AlfonsoJLuna/openhandheld-mx/Images/1.png

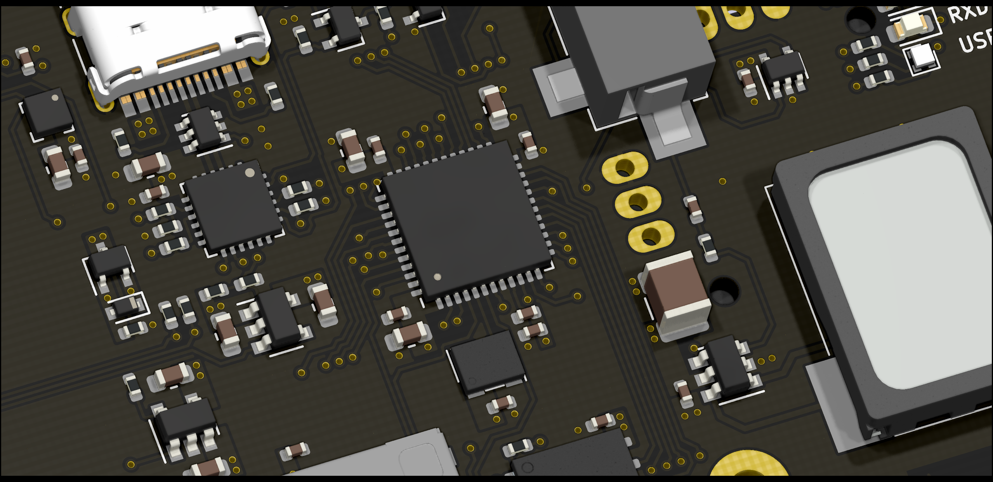
Images/1.png
