AlfonsoJLuna/openhandheld-mx/Images/3.png

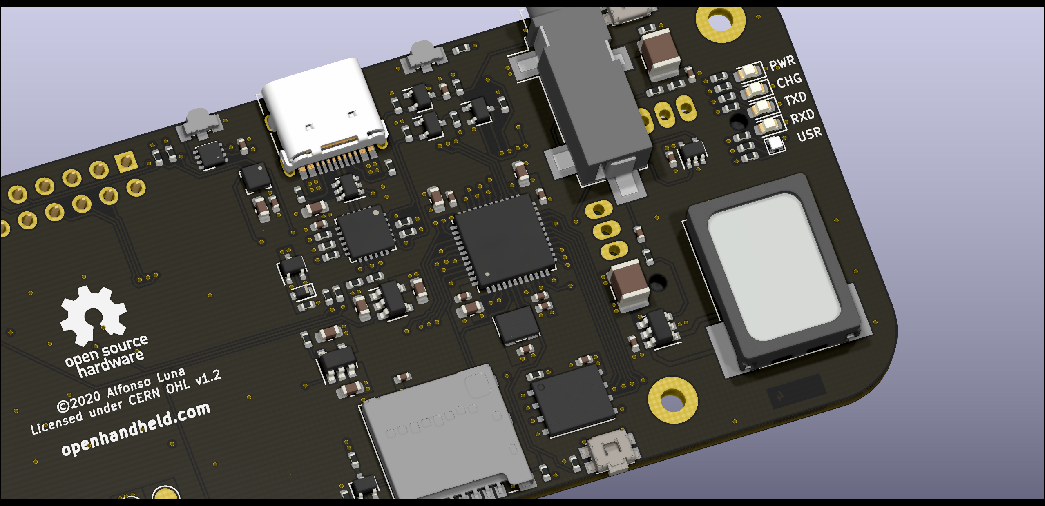
Images/3.png
