AlfonsoJLuna/openhandheld-mx/Images/4.png

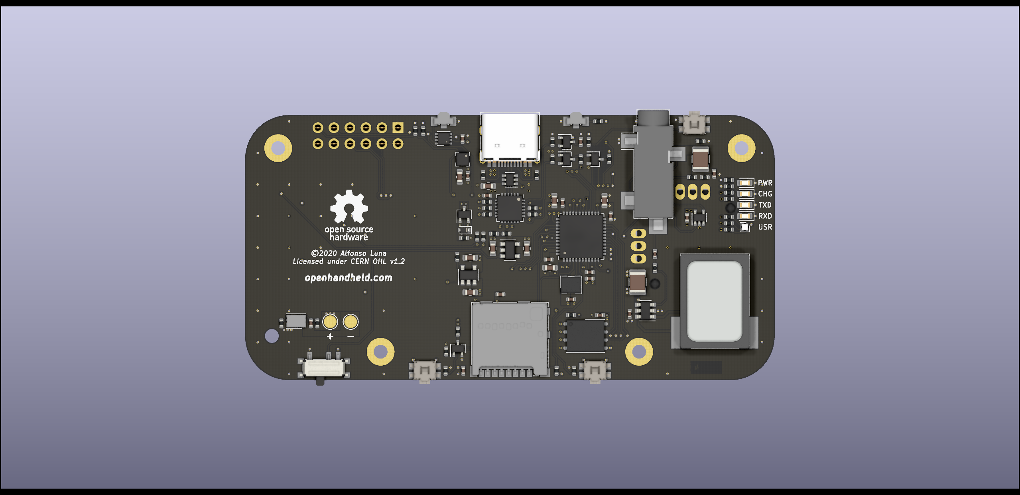
Images/4.png
