AlfonsoJLuna/openhandheld-mx/Images/5.png

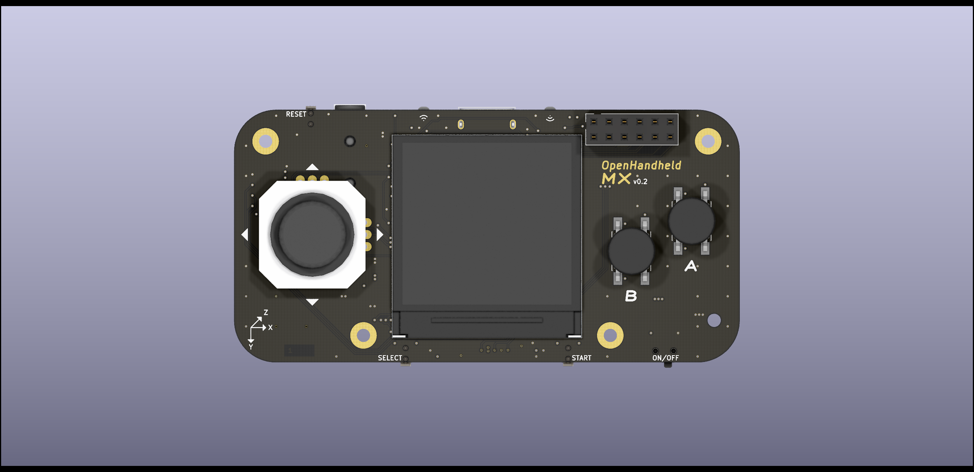
Images/5.png
