AlfonsoJLuna/openhandheld-mx/Images/8.png

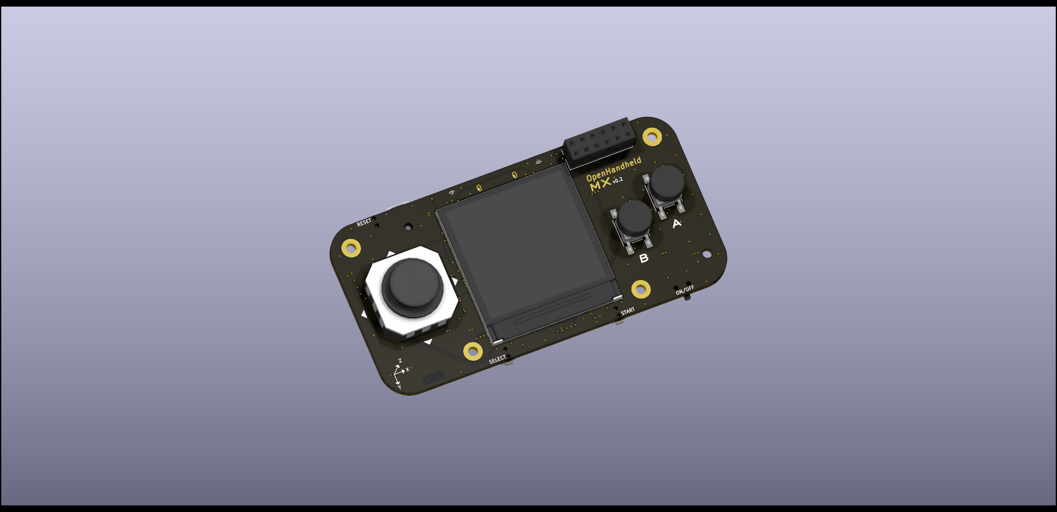
Images/8.png
