AlfonsoJLuna/openhandheld-mx/Images/10.png

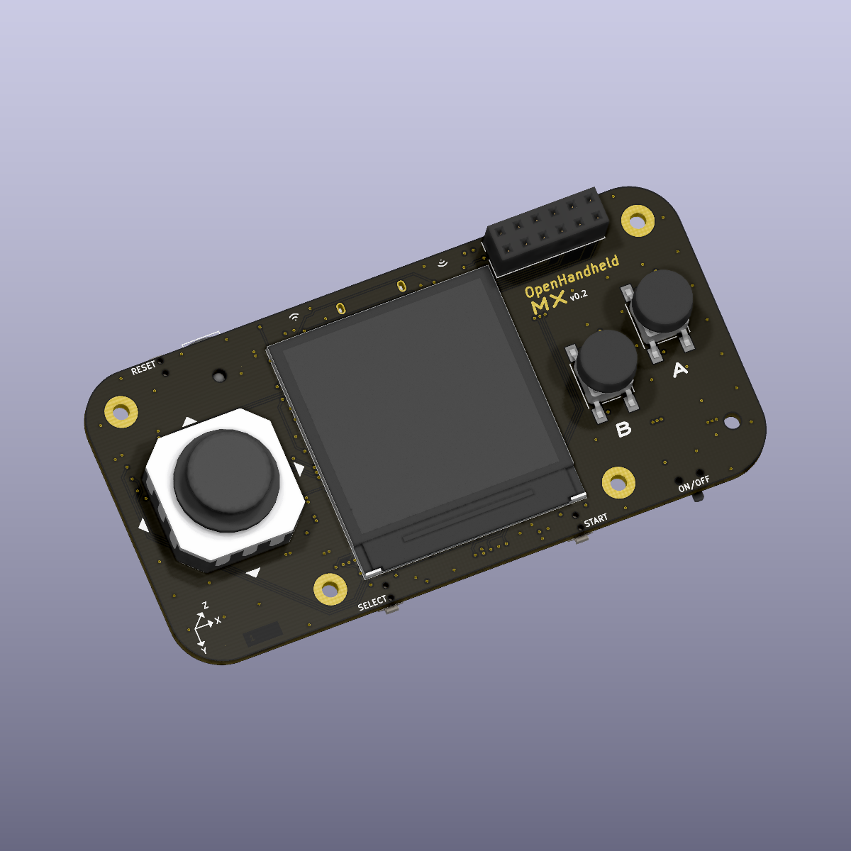
Images/10.png
