AlfonsoJLuna/openhandheld-mx/Images/11.png

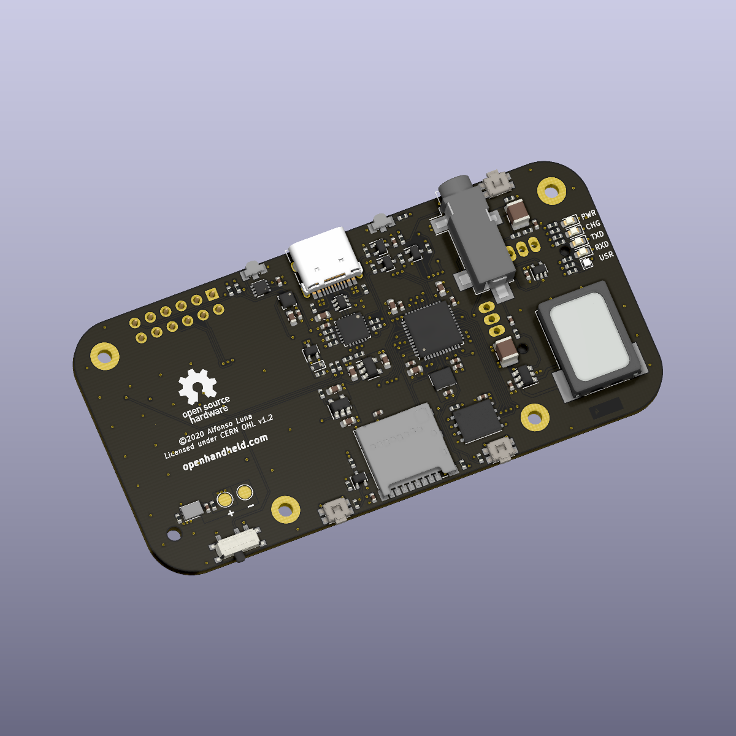
Images/11.png
