AlfonsoJLuna/openhandheld-mx/Images/12.png

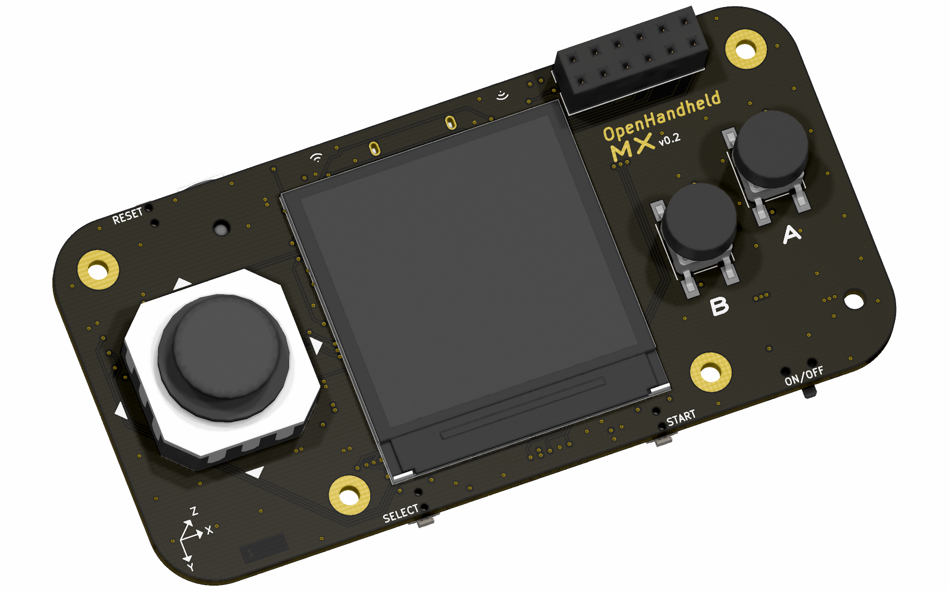
Images/12.png
