AlfonsoJLuna/openhandheld-mx/Images/13.png

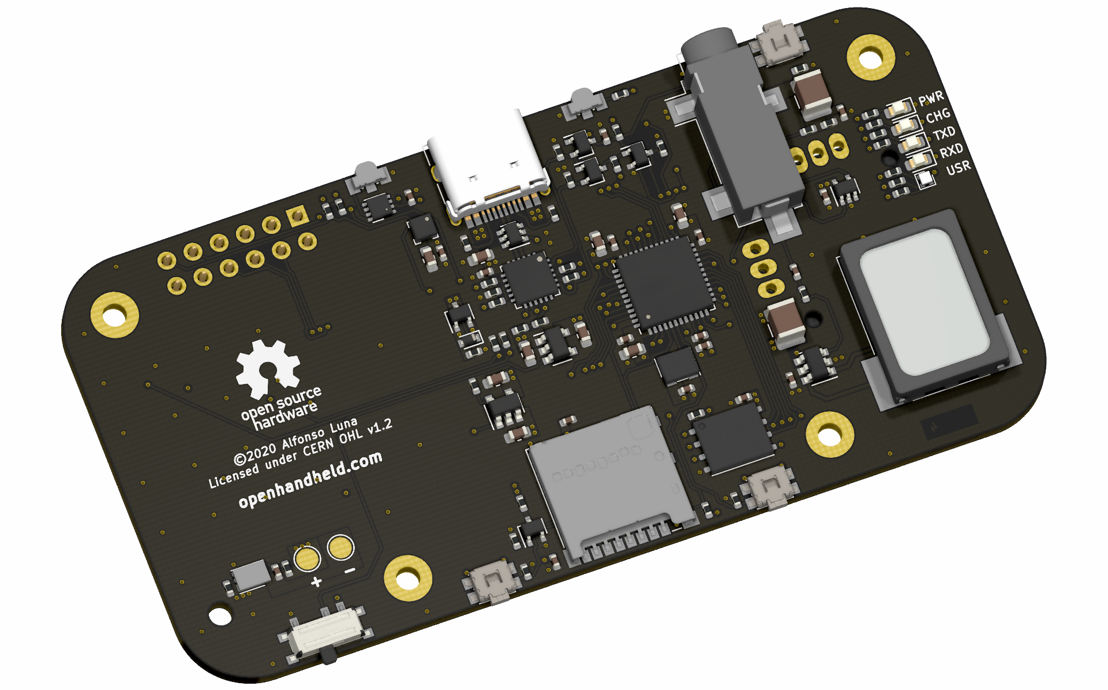
Images/13.png
