AlfonsoJLuna/openhandheld-mx/Images/16.png

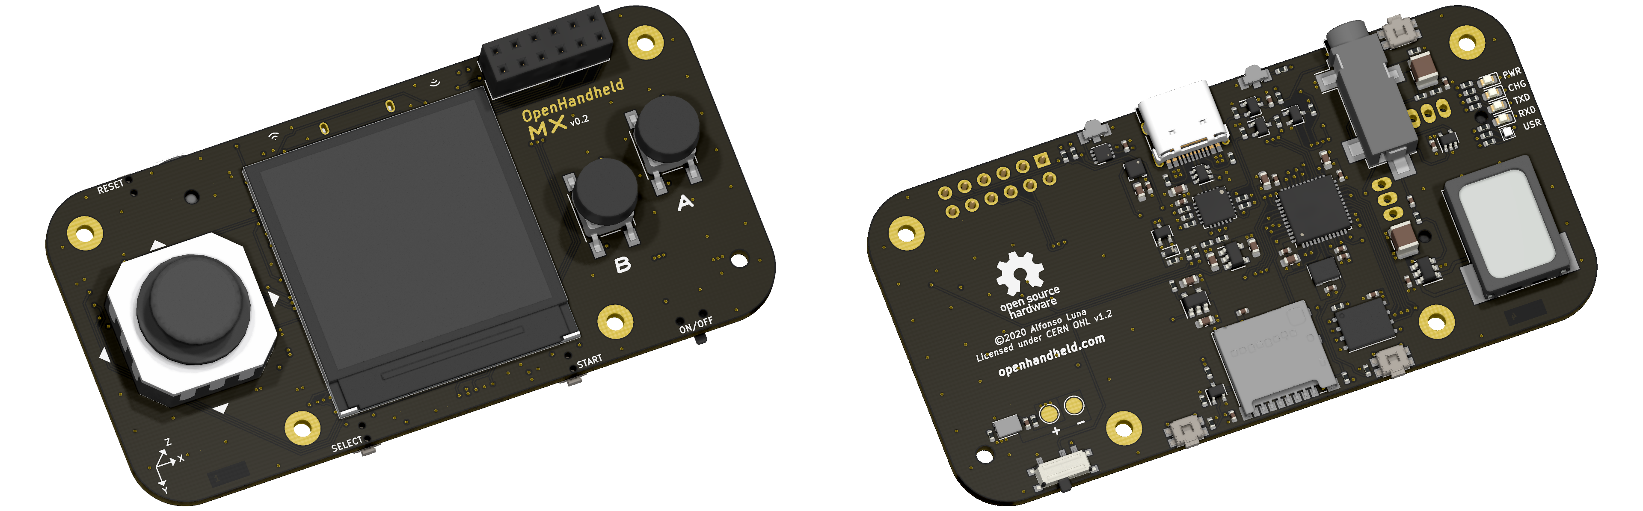
Images/16.png
