AlfonsoJLuna/openhandheld-mx/Images/18.png

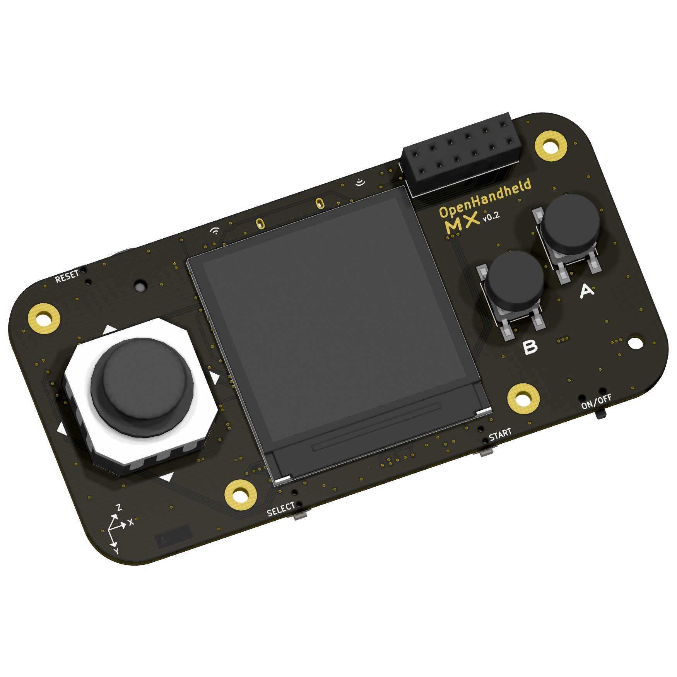
Images/18.png
