AlfonsoJLuna/openhandheld-mx/PCB/audio-simulation.asc

C1: cap; 100n
C2: cap; 100µ
C3: cap; 100n
R1: res; 16K5
R2: res; 240
R3: res; 100
R4: res; 1K8
R5: res; 16
R6: res; 10K
R7: res; 120K
R8: res; 10K
R9: res; 80K
R10: res; 1K
R11: res; 2K
R12: res; 8
U1: opamp
U2: opamp
U3: opamp
V1: voltage; SINE(1.65 1.65 2000)
Named nets: 0
STM32
Max output impedance
(DAC mode)
Headphones
Line-Out
STM32 DAC/PWM Out
Max Line-Out amplitude = (3.3V * R3) / (R2 + R3) = 1V
Max DC current = 3.3V / R2 = ~13 mA
 
Low-pass Impedance (Line-Out): R2//R3//R4//R6 = ~68 Ohm
Low-pass Impedance (Headphones): R2//R3//R4//R5 = ~13 Ohm
 
Low-pass cut-off
Line-Out: 1 / (2 * PI * 68 * 100n) = ~23 KHz
Headphones:1 / (2 * PI * 13 * 100n) = ~122KHz
High-pass Impedance (Line-Out): R4//R6 ~= 1K5 Ohm
High-pass Impedance (Headphones): R4//R5 ~= 16 Ohm
 
High-pass cut-off
Line-Out: 1 / (2 * PI * 1K5 * 100u) = ~1 Hz
Headphones: 1 / (2 * PI * 16 * 100u) = ~100 Hz
On-board Speaker
.lib opamp.sub
.tran 0 0.202 0.2
Max Gain = (80K / (120K + 10K)) * 2 = ~1.23
Max Voltage Amplitude = 1V * 1.23 = ~1.23 V
Max Peak Voltage = 1.23V / 2 = ~0.62 V
 
Max DC current = 0.62V / 8 Ohm = ~77 mA
 
High-pass cut-off: 1 / (2 * PI * (120K + 10K) * 100n) = ~12 Hz
